rfsparkling/RTL-SDR_direct_sampling_diff_amp/1.JPG

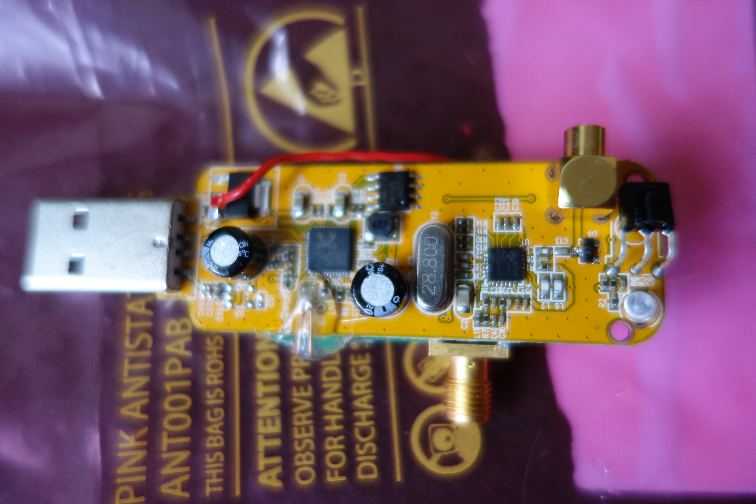
1.JPG
