rfsparkling/RTL-SDR_direct_sampling_diff_amp/2.JPG

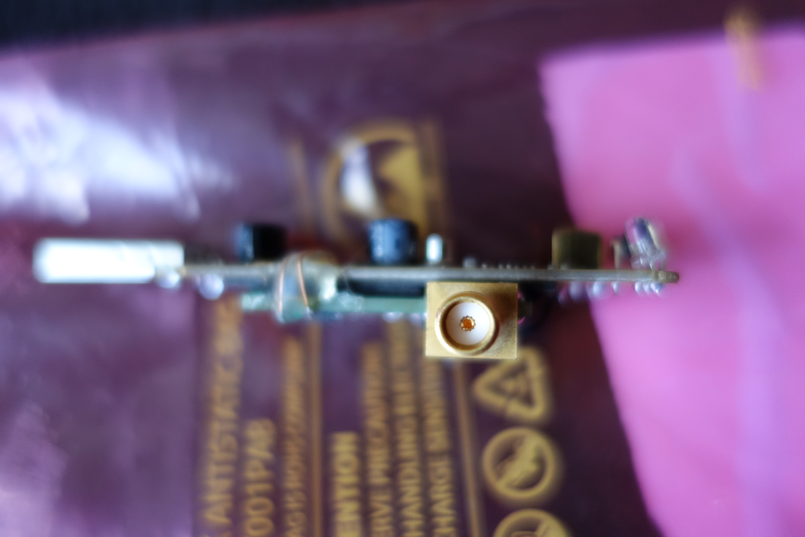
2.JPG
